bm-a/bms-connection-tester/enclosure/cad/base-isometric.png

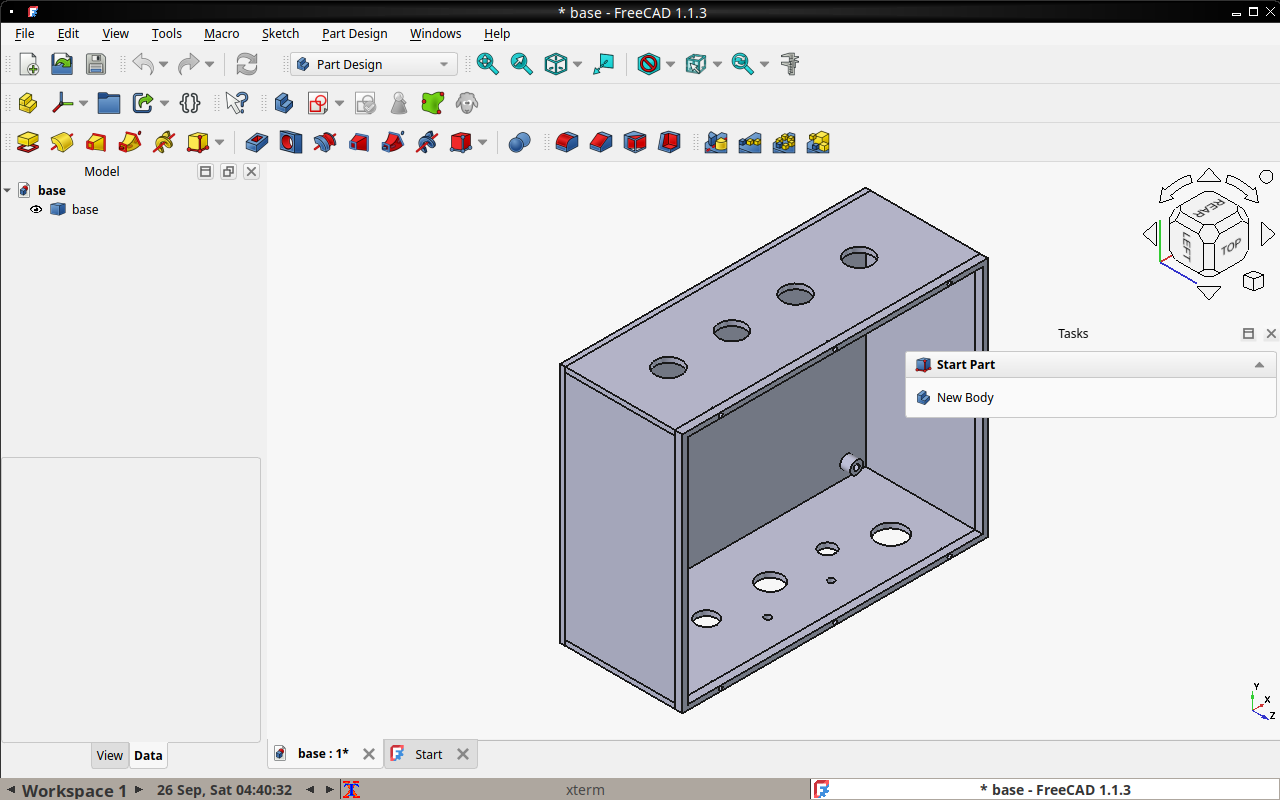
enclosure/cad/base-isometric.png
